luboslenco/armordeck/esp32/main/doom/i_system.c

//
// Copyright(C) 1993-1996 Id Software, Inc.
// Copyright(C) 2005-2014 Simon Howard
//
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
// DESCRIPTION:
//



#include <stdlib.h>
#include <stdio.h>
#include <string.h>

#include <stdarg.h>

#ifdef _WIN32
#define WIN32_LEAN_AND_MEAN
#include <windows.h>
#else
#include <unistd.h>
#endif

#ifdef ORIGCODE
#include "SDL.h"
#endif

#include "config.h"

// #include "deh_str.h"
#include "doomtype.h"
#include "m_argv.h"
#include "m_config.h"
#include "m_misc.h"
#include "i_joystick.h"
#include "i_sound.h"
#include "i_timer.h"
#include "i_video.h"

#include "i_system.h"

#include "w_wad.h"
#include "z_zone.h"

#ifdef __MACOSX__
#include <CoreFoundation/CFUserNotification.h>
#endif

#define DEFAULT_RAM 1 /* MiB */
#define MIN_RAM     1  /* MiB */


// typedef struct atexit_listentry_s atexit_listentry_t;

// struct atexit_listentry_s
// {
//     atexit_func_t func;
//     boolean run_on_error;
//     atexit_listentry_t *next;
// };

// static atexit_listentry_t *exit_funcs = NULL;

void I_AtExit(atexit_func_t func, boolean run_on_error)
{
    // atexit_listentry_t *entry;

    // entry = malloc(sizeof(*entry));

    // entry->func = func;
    // entry->run_on_error = run_on_error;
    // entry->next = exit_funcs;
    // exit_funcs = entry;
}

// Tactile feedback function, probably used for the Logitech Cyberman

void I_Tactile(int on, int off, int total)
{
}

// Zone memory auto-allocation function that allocates the zone size
// by trying progressively smaller zone sizes until one is found that
// works.

static byte *AutoAllocMemory(int *size, int default_ram, int min_ram)
{
    return NULL;

    // byte *zonemem;

    // // Allocate the zone memory.  This loop tries progressively smaller
    // // zone sizes until a size is found that can be allocated.
    // // If we used the -mb command line parameter, only the parameter
    // // provided is accepted.

    // zonemem = NULL;

    // while (zonemem == NULL)
    // {
    //     // We need a reasonable minimum amount of RAM to start.

    //     if (default_ram < min_ram)
    //     {
    //         I_Error("Unable to allocate %i MiB of RAM for zone", default_ram);
    //     }

    //     // Try to allocate the zone memory.

    //     // *size = default_ram * 1024 * 1024;
    //     //*size = 337 * 1024; ////
    //     *size = 0; ////


    //     zonemem = malloc(*size);

    //     // Failed to allocate?  Reduce zone size until we reach a size
    //     // that is acceptable.

    //     if (zonemem == NULL)
    //     {
    //         default_ram -= 1;
    //     }
    // }

    // return zonemem;
}

byte *I_ZoneBase (int *size)
{
    // return NULL;


    byte *zonemem;
    int min_ram, default_ram;
    int p;

    //!
    // @arg <mb>
    //
    // Specify the heap size, in MiB (default 16).
    //

    p = M_CheckParmWithArgs("-mb", 1);

    if (p > 0)
    {
        default_ram = atoi(myargv[p+1]);
        min_ram = default_ram;
    }
    else
    {
        default_ram = DEFAULT_RAM;
        min_ram = MIN_RAM;
    }

    zonemem = AutoAllocMemory(size, default_ram, min_ram);

    printf("zone memory: %p, %x allocated for zone\n",
           zonemem, *size);

    return zonemem;
}

void I_PrintBanner(char *msg)
{
    /*int i;
    int spaces = 35 - (strlen(msg) / 2);

    for (i=0; i<spaces; ++i)
        putchar(' ');

    puts(msg);*/
}

void I_PrintDivider(void)
{
    /*int i;

    for (i=0; i<75; ++i)
    {
        putchar('=');
    }

    putchar('\n');*/
}

void I_PrintStartupBanner(char *gamedescription)
{
    //I_PrintDivider();
    //I_PrintBanner(gamedescription);
    //I_PrintDivider();

    // printf(
    // " " PACKAGE_NAME " is free software, covered by the GNU General Public\n"
    // " License.  There is NO warranty; not even for MERCHANTABILITY or FITNESS\n"
    // " FOR A PARTICULAR PURPOSE. You are welcome to change and distribute\n"
    // " copies under certain conditions. See the source for more information.\n");

    //I_PrintDivider();
}

//
// I_ConsoleStdout
//
// Returns true if stdout is a real console, false if it is a file
//

boolean I_ConsoleStdout(void)
{
    return 0;
// #ifdef _WIN32
//     // SDL "helpfully" always redirects stdout to a file.
//     return 0;
// #else
// #if ORIGCODE
//     return isatty(fileno(stdout));
// #else
// 	return 0;
// #endif
// #endif
}

//
// I_Init
//
/*
void I_Init (void)
{
    I_CheckIsScreensaver();
    I_InitTimer();
    I_InitJoystick();
}
void I_BindVariables(void)
{
    I_BindVideoVariables();
    I_BindJoystickVariables();
    I_BindSoundVariables();
}
*/

//
// I_Quit
//

void I_Quit (void)
{
//     atexit_listentry_t *entry;

//     // Run through all exit functions

//     entry = exit_funcs;

//     while (entry != NULL)
//     {
//         entry->func();
//         entry = entry->next;
//     }

// #if ORIGCODE
//     SDL_Quit();

//     exit(0);
// #endif
}

//
// I_Error
//

// static boolean already_quitting = false;

void I_Error (char *error, ...)
{
    // char msgbuf[512];
    va_list argptr;
    // atexit_listentry_t *entry;
    // boolean exit_gui_popup;

    // if (already_quitting)
    // {
//         fprintf(stderr, "Warning: recursive call to I_Error detected.\n");
// #if ORIGCODE
//         exit(-1);
// #endif
    // }
    // else
    // {
    //     already_quitting = true;
    // }

    // Message first.
    va_start(argptr, error);
    // fprintf(stderr, "\nError: ");
    vfprintf(stderr, error, argptr);
    fprintf(stderr, "\n\n");
    va_end(argptr);
    fflush(stderr);

    // Write a copy of the message into buffer.
    // va_start(argptr, error);
    // memset(msgbuf, 0, sizeof(msgbuf));
    // M_vsnprintf(msgbuf, sizeof(msgbuf), error, argptr);
    // va_end(argptr);

    // Shutdown. Here might be other errors.

//     entry = exit_funcs;

//     while (entry != NULL)
//     {
//         if (entry->run_on_error)
//         {
//             entry->func();
//         }

//         entry = entry->next;
//     }

//     exit_gui_popup = !M_ParmExists("-nogui");

//     // Pop up a GUI dialog box to show the error message, if the
//     // game was not run from the console (and the user will
//     // therefore be unable to otherwise see the message).
//     if (exit_gui_popup && !I_ConsoleStdout())
#ifdef _WIN32
    {
        char msgbuf[512];
        va_start(argptr, error);
        memset(msgbuf, 0, sizeof(msgbuf));
        M_vsnprintf(msgbuf, sizeof(msgbuf), error, argptr);
        va_end(argptr);

        wchar_t wmsgbuf[512];

        MultiByteToWideChar(CP_ACP, 0,
                            msgbuf, strlen(msgbuf) + 1,
                            wmsgbuf, sizeof(wmsgbuf));

        MessageBoxW(NULL, wmsgbuf, L"", MB_OK);
    }
// #elif defined(__MACOSX__)
//     {
//         CFStringRef message;
// 	int i;

// 	// The CoreFoundation message box wraps text lines, so replace
// 	// newline characters with spaces so that multiline messages
// 	// are continuous.

// 	for (i = 0; msgbuf[i] != '\0'; ++i)
//         {
//             if (msgbuf[i] == '\n')
//             {
//                 msgbuf[i] = ' ';
//             }
//         }

//         message = CFStringCreateWithCString(NULL, msgbuf,
//                                             kCFStringEncodingUTF8);

//         CFUserNotificationDisplayNotice(0,
//                                         kCFUserNotificationCautionAlertLevel,
//                                         NULL,
//                                         NULL,
//                                         NULL,
//                                         CFSTR(PACKAGE_STRING),
//                                         message,
//                                         NULL);
//     }
// #else
//     {
//         ZenityErrorBox(msgbuf);
//     }
#endif

//     // abort();
// #if ORIGCODE
//     SDL_Quit();

//     exit(-1);
// #else
//     while (true)
//     {
//     }
// #endif
}

boolean I_GetMemoryValue(unsigned int offset, void *value, int size)
{
    // static boolean firsttime = true;

    // if (firsttime)
    // {
    //     int p, i, val;

    //     firsttime = false;
    //     i = 0;

    //     //!
    //     // @category compat
    //     // @arg <version>
    //     //
    //     // Specify DOS version to emulate for NULL pointer dereference
    //     // emulation.  Supported versions are: dos622, dos71, dosbox.
    //     // The default is to emulate DOS 7.1 (Windows 98).
    //     //

    //     p = M_CheckParmWithArgs("-setmem", 1);

    //     if (p > 0)
    //     {
    //         if (!strcasecmp(myargv[p + 1], "dos622"))
    //         {
    //             dos_mem_dump = mem_dump_dos622;
    //         }
    //         if (!strcasecmp(myargv[p + 1], "dos71"))
    //         {
    //             dos_mem_dump = mem_dump_win98;
    //         }
    //         else if (!strcasecmp(myargv[p + 1], "dosbox"))
    //         {
    //             dos_mem_dump = mem_dump_dosbox;
    //         }
    //         else
    //         {
    //             for (i = 0; i < DOS_MEM_DUMP_SIZE; ++i)
    //             {
    //                 ++p;

    //                 if (p >= myargc || myargv[p][0] == '-')
    //                 {
    //                     break;
    //                 }

    //                 M_StrToInt(myargv[p], &val);
    //                 mem_dump_custom[i++] = (unsigned char) val;
    //             }

    //             dos_mem_dump = mem_dump_custom;
    //         }
    //     }
    // }

    // switch (size)
    // {
    // case 1:
    //     *((unsigned char *) value) = dos_mem_dump[offset];
    //     return true;
    // case 2:
    //     *((unsigned short *) value) = dos_mem_dump[offset]
    //                                 | (dos_mem_dump[offset + 1] << 8);
    //     return true;
    // case 4:
    //     *((unsigned int *) value) = dos_mem_dump[offset]
    //                               | (dos_mem_dump[offset + 1] << 8)
    //                               | (dos_mem_dump[offset + 2] << 16)
    //                               | (dos_mem_dump[offset + 3] << 24);
    //     return true;
    // }

    return false;
}
